WeaselJones/DinoCalc/Hardware/EagleCad files/DinoCalc_1v0.sch

## EAGLE design Hardware/EagleCad files/DinoCalc_1v0.sch (2013-03-11)

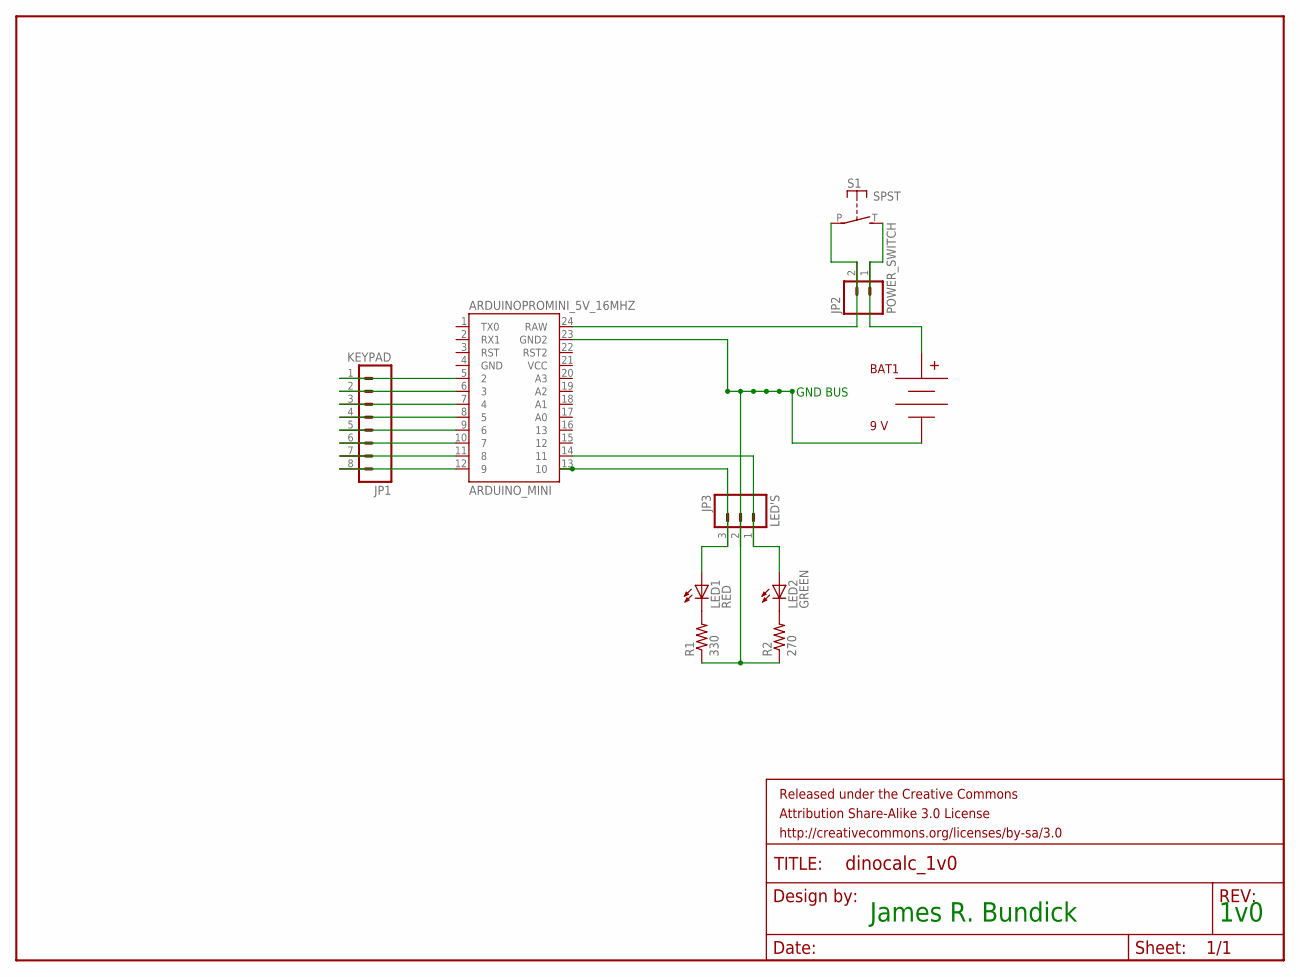
[picture p10: schematic DinoCalc_1v0.sch]

Parts:
ARDUINOPROMINI_5V_16MHZ: ARDUINO_MINI
BAT1: 9 V; BC9VPC
FRAME1: FRAME-LETTER; CREATIVE_COMMONS
JP1: KEYPAD; 1X08_LONGPADS
JP2: POWER_SWITCH; 1X02_LONGPADS
JP3: LED'S; 1X03_LONGPADS
LED1: RED; LED5MM
LED2: GREEN; LED5MM
R1: 330; AXIAL-0.4
R2: 270; AXIAL-0.4
S1: SPST; JUDCOSPST

Connections:
unnamed: ARDUINOPROMINI_5V_16MHZ.5 (2), JP1.1
unnamed: ARDUINOPROMINI_5V_16MHZ.6 (3), JP1.2
unnamed: ARDUINOPROMINI_5V_16MHZ.7 (4), JP1.3
unnamed: ARDUINOPROMINI_5V_16MHZ.8 (5), JP1.4
unnamed: ARDUINOPROMINI_5V_16MHZ.9 (6), JP1.5
unnamed: ARDUINOPROMINI_5V_16MHZ.10 (7), JP1.6
unnamed: ARDUINOPROMINI_5V_16MHZ.11 (8), JP1.7
unnamed: ARDUINOPROMINI_5V_16MHZ.12 (9), JP1.8
unnamed: ARDUINOPROMINI_5V_16MHZ.23 (GND2), BAT1.V-, JP3.2, R1.P$1 (1), R2.P$1 (1)
unnamed: BAT1.V+, JP2.1, S1.T (S)
unnamed: ARDUINOPROMINI_5V_16MHZ.24 (RAW), JP2.2, S1.P
unnamed: LED1.K (C), R1.P$2 (2)
unnamed: LED2.K (C), R2.P$2 (2)
unnamed: ARDUINOPROMINI_5V_16MHZ.14 (11), JP3.1, LED2.A
unnamed: ARDUINOPROMINI_5V_16MHZ.13 (10), JP3.3, LED1.A

Notes on the sheet:
GND BUS
James R. Bundick
1v0
